WolfgangFahl/nicesprinkler/images/20260815_185550_lawn_about_page.png

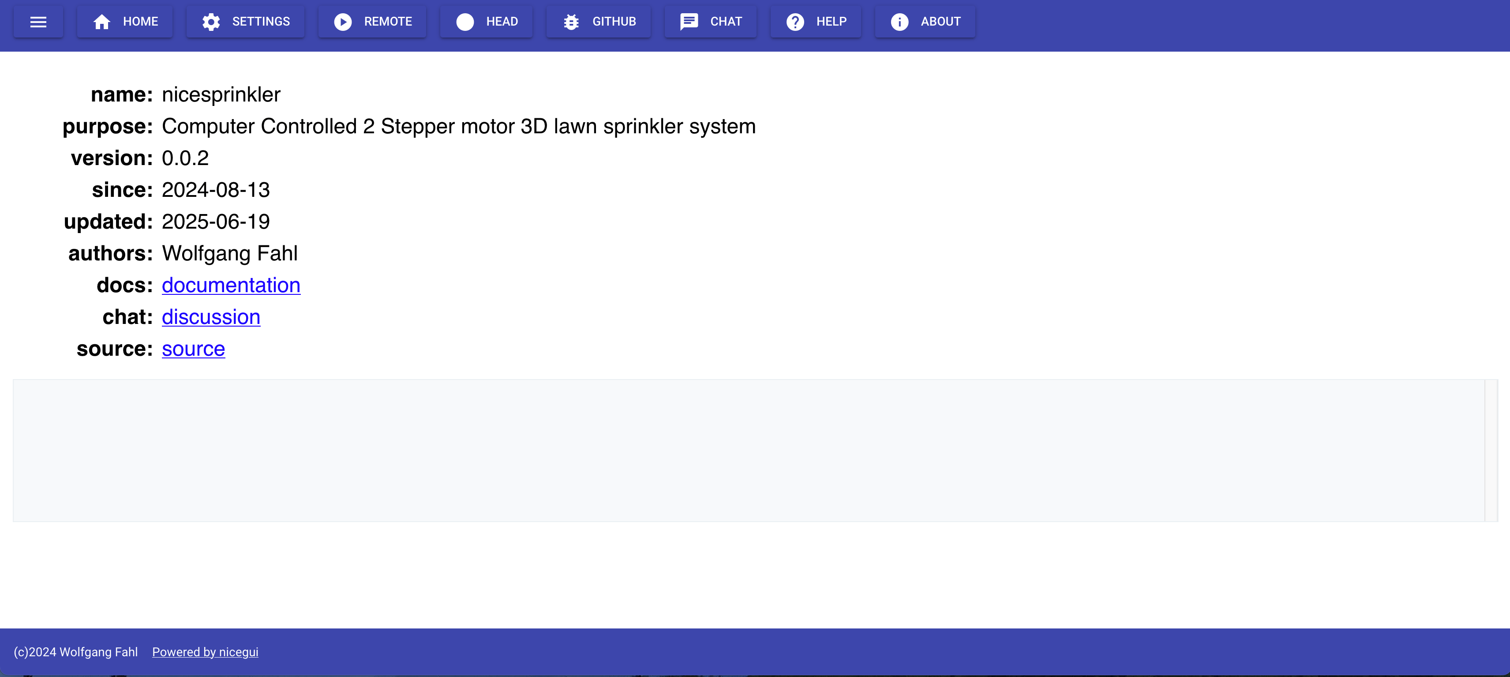
images/20260815_185550_lawn_about_page.png
