WolfgangFahl/nicesprinkler/images/20260815_185858_lawn_head_broken.png

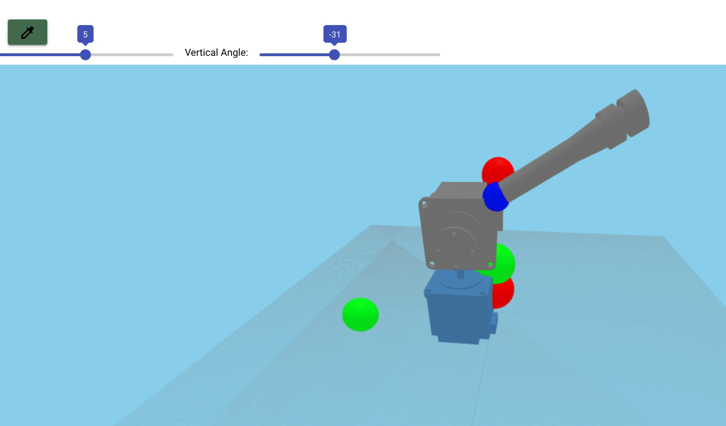
images/20260815_185858_lawn_head_broken.png
