WolfgangFahl/nicesprinkler/images/20260815_193547_lawn_remote_camera_page.png

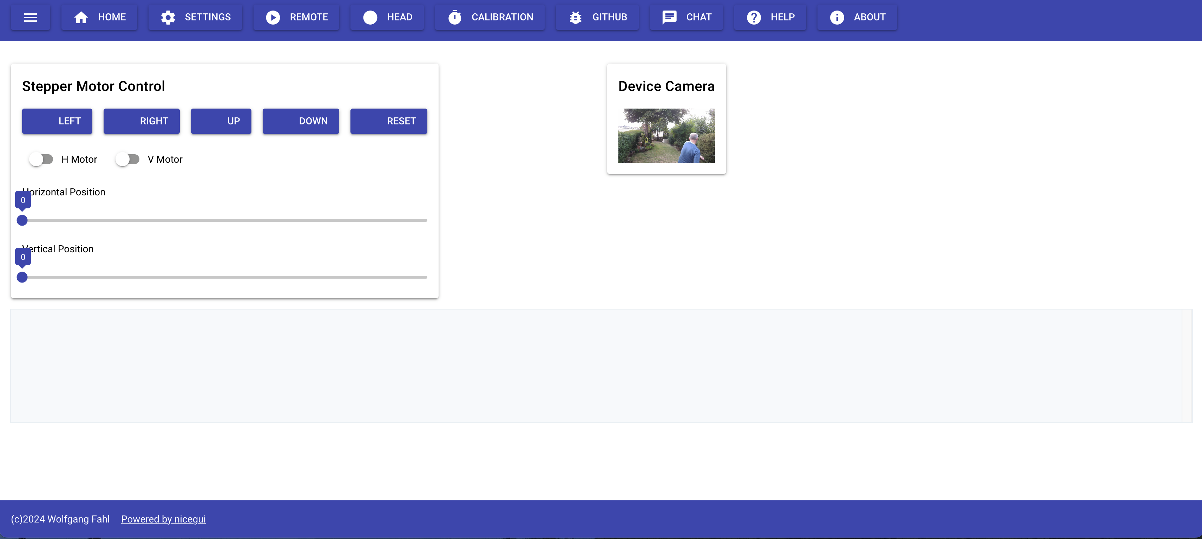
images/20260815_193547_lawn_remote_camera_page.png
