WolfgangFahl/nicesprinkler/images/20260815_194158_lawn_remote_camera2.png

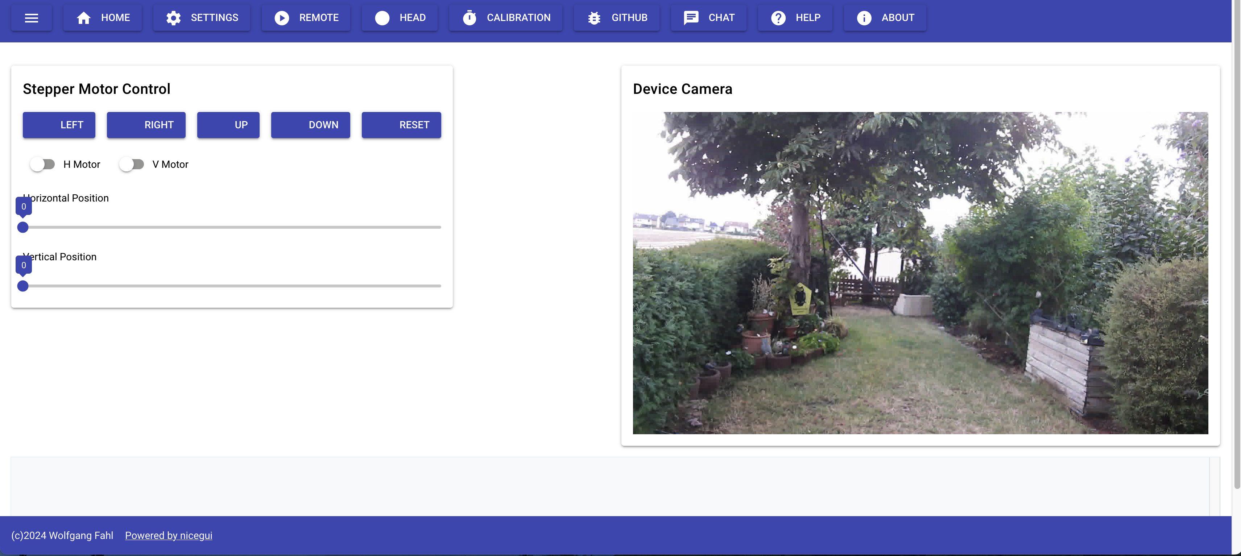
images/20260815_194158_lawn_remote_camera2.png
