WolfgangFahl/nicesprinkler/images/20260815_202555_lawn_remote_record.png

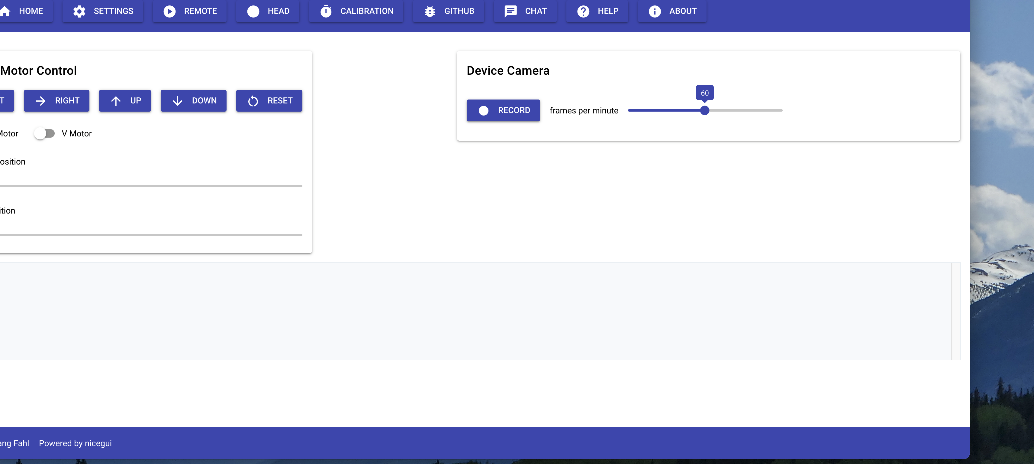
images/20260815_202555_lawn_remote_record.png
