WolfgangFahl/nicesprinkler/images/20260816_085040_00203_devcam.jpg

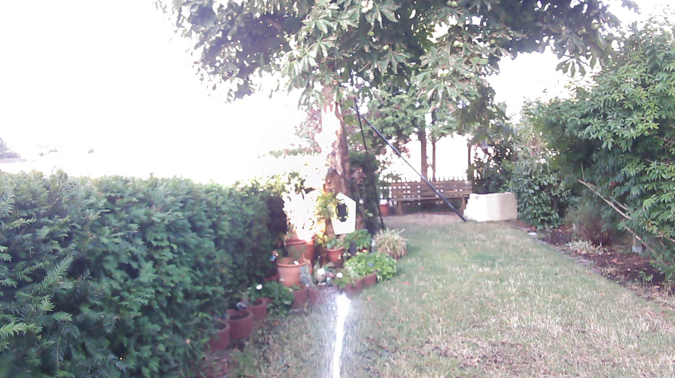
images/20260816_085040_00203_devcam.jpg
