WolfgangFahl/nicesprinkler/images/20260816_085052_00214_devcam.jpg

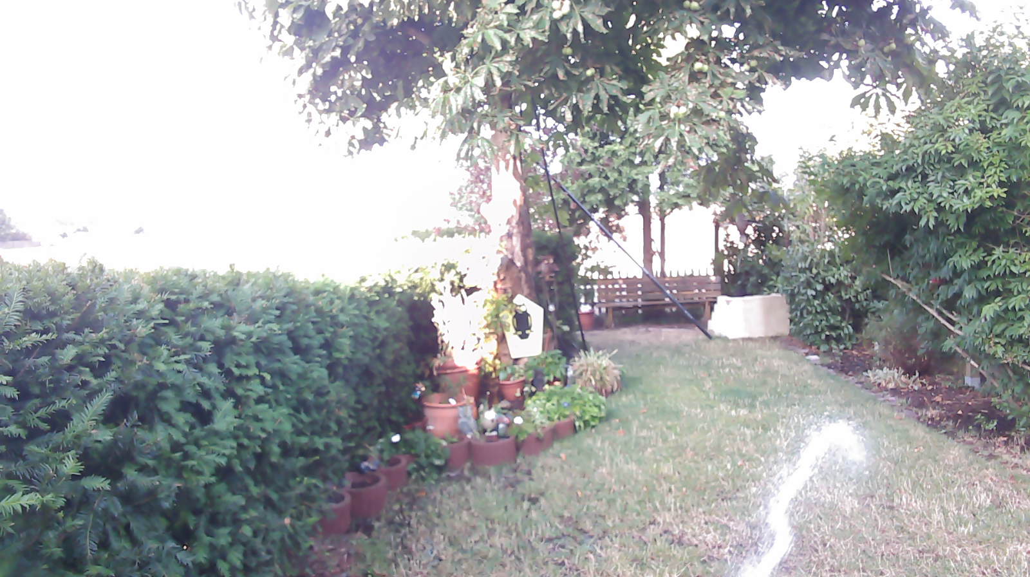
images/20260816_085052_00214_devcam.jpg
