WolfgangFahl/nicesprinkler/images/20260815_191909_lawn_calibration_page.png

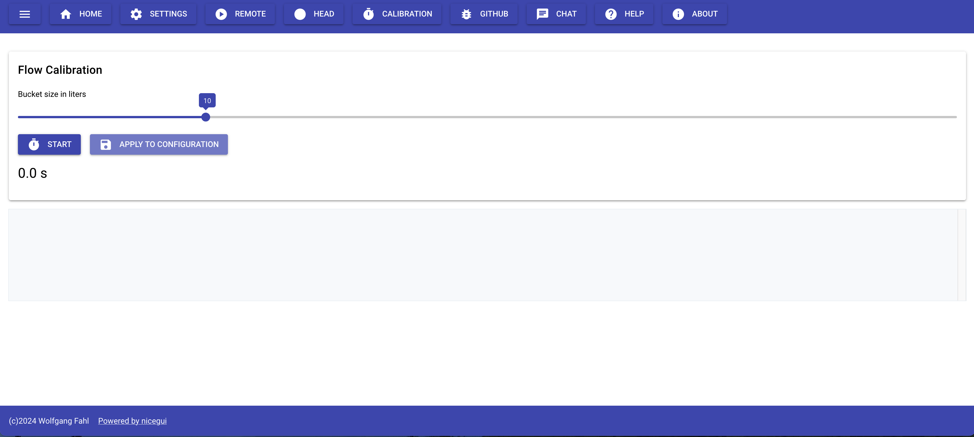
images/20260815_191909_lawn_calibration_page.png
