WolfgangFahl/nicesprinkler/images/20260815_192657_calibration_traceback.jpg

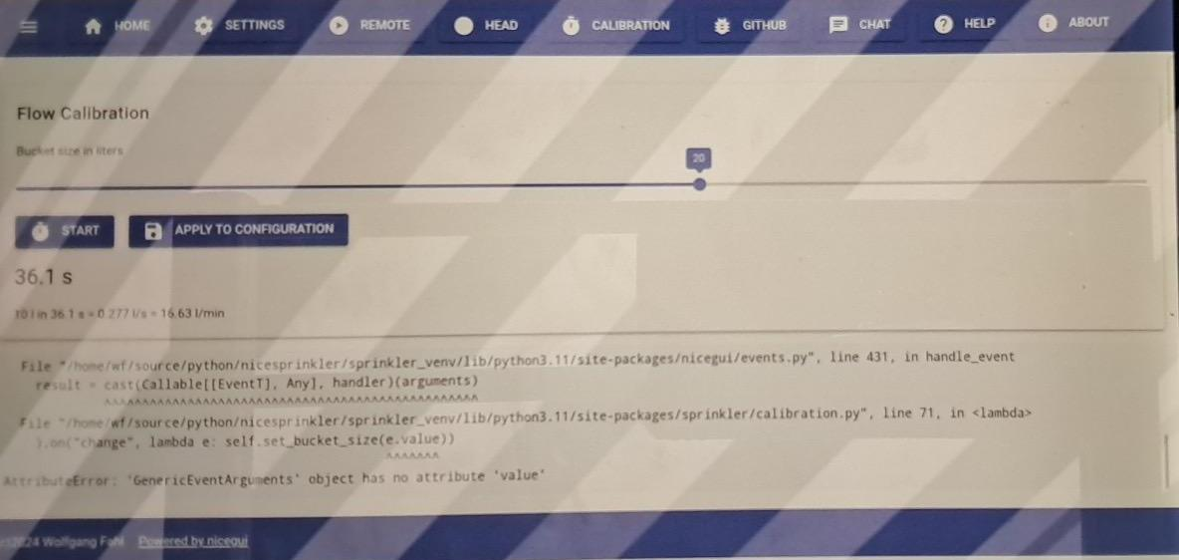
images/20260815_192657_calibration_traceback.jpg
