WolfgangFahl/nicesprinkler/sprinkler/webserver.py

"""
Created on 2024-08-13

@author: wf
"""

import os
import shutil

from ngwidgets.input_webserver import InputWebserver, InputWebSolution
from ngwidgets.webserver import WebserverConfig
from nicegui import Client, app, ui

from sprinkler.api import SprinklerApi
from sprinkler.calibration import CalibrationView
from sprinkler.camera import CameraView
from sprinkler.sprinkler_core import SprinklerConfig, SprinklerSystem
from sprinkler.sprinkler_head import SprinklerHeadView
from sprinkler.sprinkler_sim import SprinklerSimulation
from sprinkler.stepper_view import StepperView
from sprinkler.version import Version


class NiceSprinklerWebServer(InputWebserver):
    """WebServer class that manages the server and handles Sprinkler operations."""

    @classmethod
    def get_config(cls) -> WebserverConfig:
        config = WebserverConfig(
            copy_right=Version.copy_right,
            version=Version(),
            default_port=9848,
            short_name="nicesprinkler",
        )
        server_config = WebserverConfig.get(config)
        server_config.solution_class = NiceSprinklerSolution
        return server_config

    def __init__(self):
        """Constructs all the necessary attributes for the WebServer object."""
        InputWebserver.__init__(self, config=NiceSprinklerWebServer.get_config())
        self.sprinkler_system = None
        # the frame route has to exist before the server starts
        CameraView.add_route()

        @ui.page("/remote")
        async def remote(client: Client):
            return await self.page(client, NiceSprinklerSolution.remote)

        @ui.page("/sprinkler-head")
        async def sprinkler_head(client: Client):
            return await self.page(client, NiceSprinklerSolution.sprinkler_head)

        @ui.page("/calibration")
        async def calibration(client: Client):
            return await self.page(client, NiceSprinklerSolution.calibration)

    def configure_run(self):
        """
        Configure the run based on command line arguments
        """
        if hasattr(self.args, "root_path"):
            self.root_path = self.args.root_path
        else:
            self.root_path = self.config.config_path
        self.config_path = self.installation_path(
            self.args.config, "example_config.yaml"
        )
        self.stl_path = self.installation_path(self.args.stl, "example_garden.stl")

        # Create SprinklerSystem
        self.sprinkler_system = SprinklerSystem(self.config_path, self.stl_path)
        CameraView.camera.rotation = getattr(
            self.sprinkler_system.config, "camera_rotation", 0
        )
        self.api = SprinklerApi(self, self.root_path)
        self.api.add_routes()
        stl_directory = os.path.dirname(self.stl_path)

        # Add the static files route for serving the STL files
        app.add_static_files("/examples", stl_directory)
        pass

    def installation_path(self, arg_path: str, example_name: str) -> str:
        """
        Get the installation path for the given argument, seeded from the example.

        An absolute argument is used as it stands. A relative one is resolved
        against the installation directory of this solution; when the file is
        missing there the example that ships with the package is copied in once,
        so an update never touches the file the installation works with.

        Args:
            arg_path: the path as given on the command line
            example_name: the name of the example to copy in when nothing exists

        Returns:
            the absolute path of the file to be used
        """
        path = arg_path
        if not os.path.isabs(path):
            path = os.path.join(self.root_path, path)
        if not os.path.exists(path):
            example = os.path.join(self.examples_path(), example_name)
            os.makedirs(os.path.dirname(path), exist_ok=True)
            shutil.copy(example, path)
        return path

    @classmethod
    def examples_path(cls) -> str:
        path = os.path.join(os.path.dirname(__file__), "../nicesprinkler_examples")
        path = os.path.abspath(path)
        return path


class NiceSprinklerSolution(InputWebSolution):
    """
    the NiceSprinkler solution
    """

    def __init__(self, webserver: NiceSprinklerWebServer, client: Client):
        """
        Initialize the solution

        Args:
            webserver (NiceSprinklerWebServer): The webserver instance associated with this context.
            client (Client): The client instance this context is associated with.
        """
        super().__init__(webserver, client)
        self.simulation = None

    def configure_menu(self):
        """
        configure additional non-standard menu entries
        """
        self.link_button(name="remote", icon_name="play_circle", target="/remote")
        self.link_button(name="head", icon_name="circle", target="/sprinkler-head")
        self.link_button(name="calibration", icon_name="timer", target="/calibration")

    async def remote(self):
        def setup_remote():
            with ui.row().classes("w-full no-wrap"):
                with ui.column().classes("w-1/2"):
                    self.stepper_control = StepperView(
                        self, self.webserver.sprinkler_system
                    )
                    self.stepper_control.setup_ui()
                with ui.column().classes("w-1/2"):
                    self.camera_view = CameraView(self, stepper=self.stepper_control)
                    self.camera_view.setup_ui()

        await self.setup_content_div(setup_remote)

    async def sprinkler_head(self):
        def setup_sprinkler_head():
            self.sphv = SprinklerHeadView(self, self.webserver.sprinkler_system)
            self.sphv.setup_ui()

        await self.setup_content_div(setup_sprinkler_head)

    async def calibration(self):
        def setup_calibration():
            self.calibration_view = CalibrationView(
                self, self.webserver.sprinkler_system
            )
            self.calibration_view.setup_ui()

        await self.setup_content_div(setup_calibration)

    async def home(self):
        """Generates the home page with a 3D viewer and controls for the sprinkler."""
        self.setup_menu()
        with ui.column():
            self.simulation = SprinklerSimulation(self, self.webserver.sprinkler_system)
            self.simulation.setup_scene_frame()

        await self.setup_footer()

    def configure_settings(self):
        """Generates the settings page with options to modify sprinkler configuration."""
        config_str = self.webserver.sprinkler_system.config.to_yaml()
        ui.textarea(
            "Configuration", value=config_str, on_change=self.update_config
        ).classes("w-full")

    def update_config(self, e):
        """Updates the simulation configuration based on user input."""
        try:
            new_config = SprinklerConfig.from_yaml(e.value)
            self.webserver.sprinkler_system.config = new_config
            self.simulation.sprinkler_system = self.webserver.sprinkler_system
            self.reset_simulation()
            ui.notify("Configuration updated successfully")
        except Exception as ex:
            ui.notify(f"Error updating configuration: {str(ex)}", color="red")
